LoaderB0T/Bl3-EchoCom/img/img (6).jpg

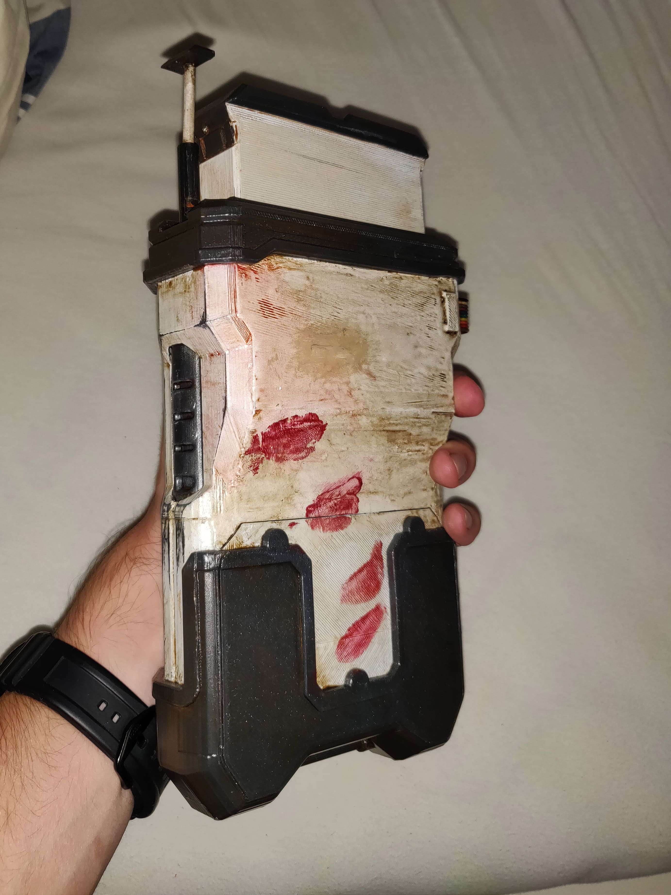
img/img (6).jpg
