LoaderB0T/Bl3-EchoCom/stl/electronics version/echoCom ButtonSquare.stl

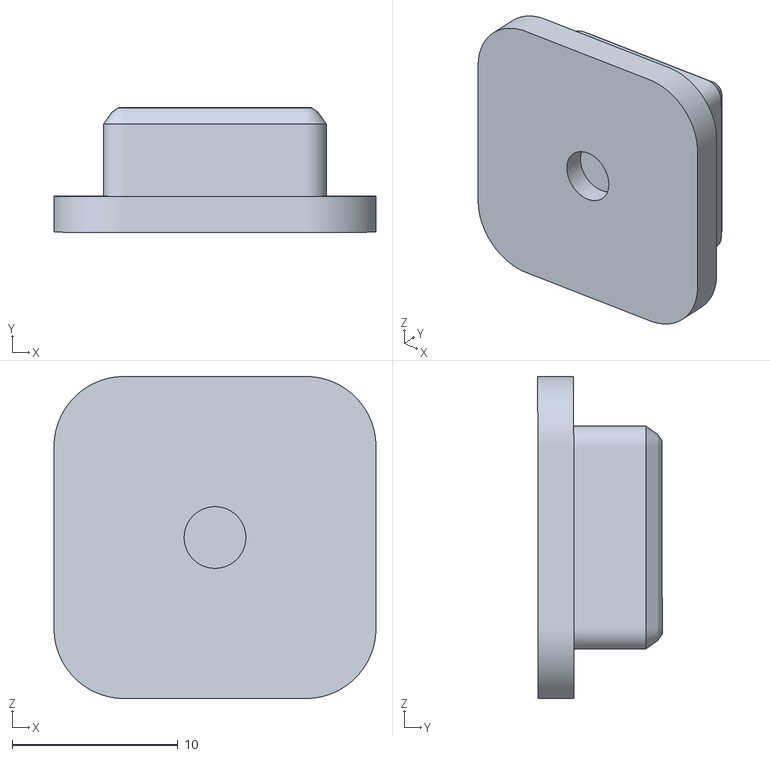
[picture p35: CAD file, 2020-08-17]
stl/electronics version/echoCom ButtonSquare.stl
19.4 x 7.51 x 19.4
